ariwijayaputra/PeakGroundAcceleration/mqtt esp8266 accel/web/blueAbstract.jpg

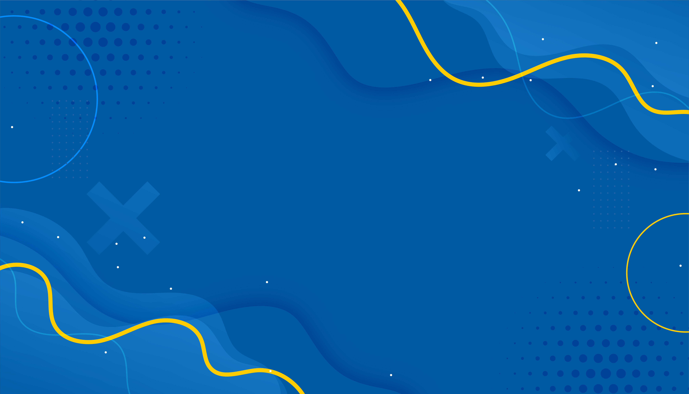
mqtt esp8266 accel/web/blueAbstract.jpg
