ariwijayaputra/PeakGroundAcceleration/mqtt esp8266 accel/web/dist/img/boxed-bg.jpg

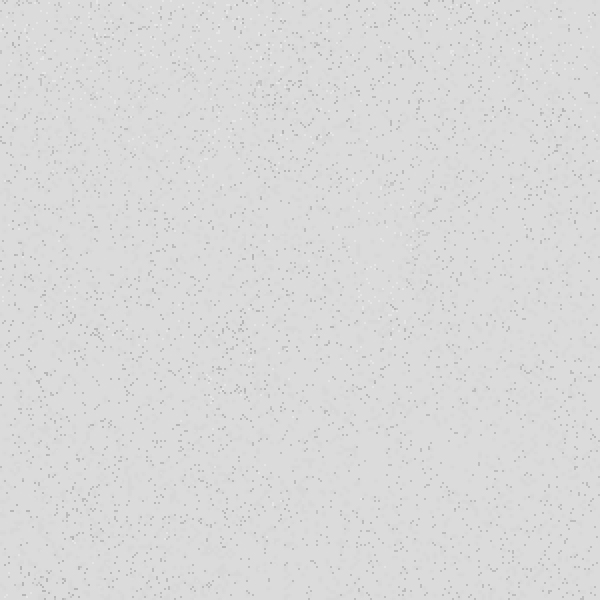
mqtt esp8266 accel/web/dist/img/boxed-bg.jpg
