ariwijayaputra/PeakGroundAcceleration/mqtt esp8266 accel/web/dist/img/photo1.png

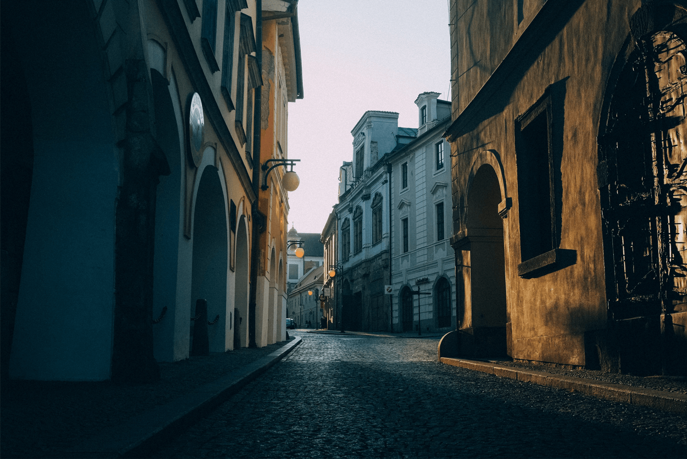
mqtt esp8266 accel/web/dist/img/photo1.png
