ariwijayaputra/PeakGroundAcceleration/mqtt esp8266 accel/web/dist/img/photo2.png

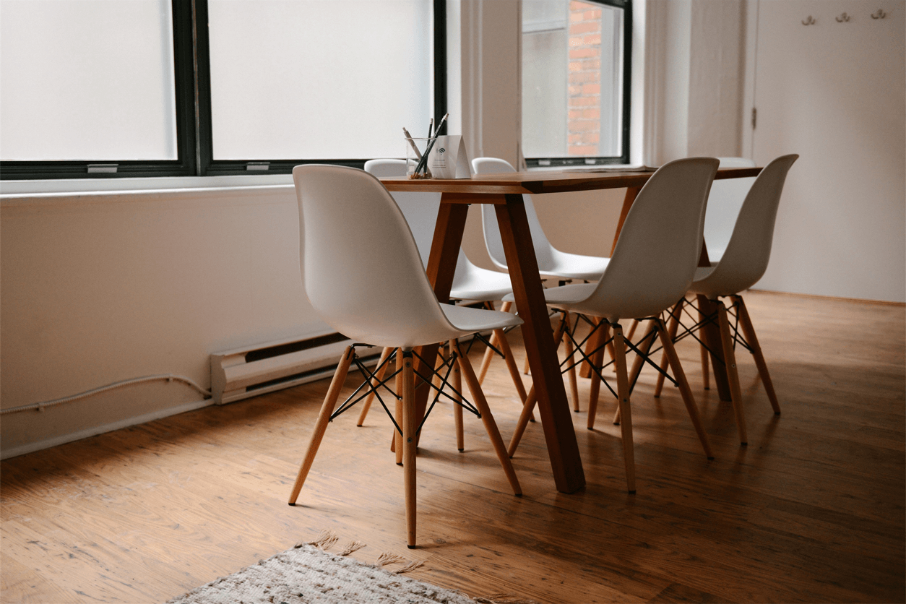
mqtt esp8266 accel/web/dist/img/photo2.png
