ariwijayaputra/PeakGroundAcceleration/mqtt esp8266 accel/web/dist/img/photo3.jpg

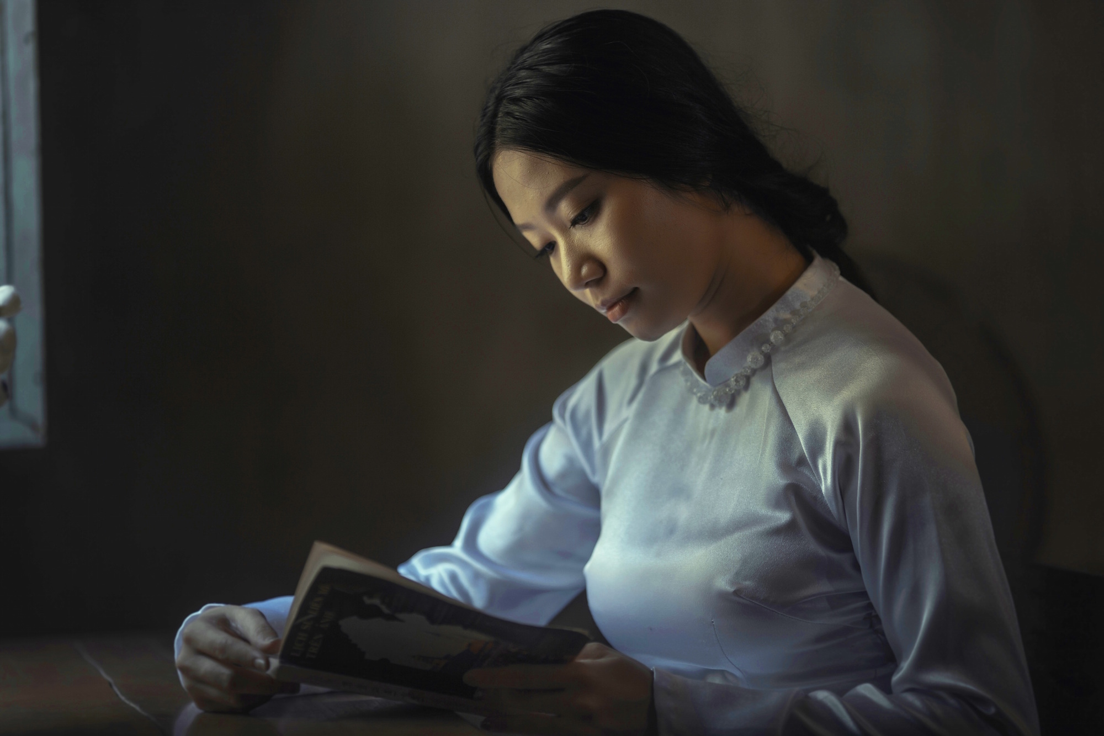
mqtt esp8266 accel/web/dist/img/photo3.jpg
