ariwijayaputra/PeakGroundAcceleration/mqtt esp8266 accel/web/dist/img/photo4.jpg

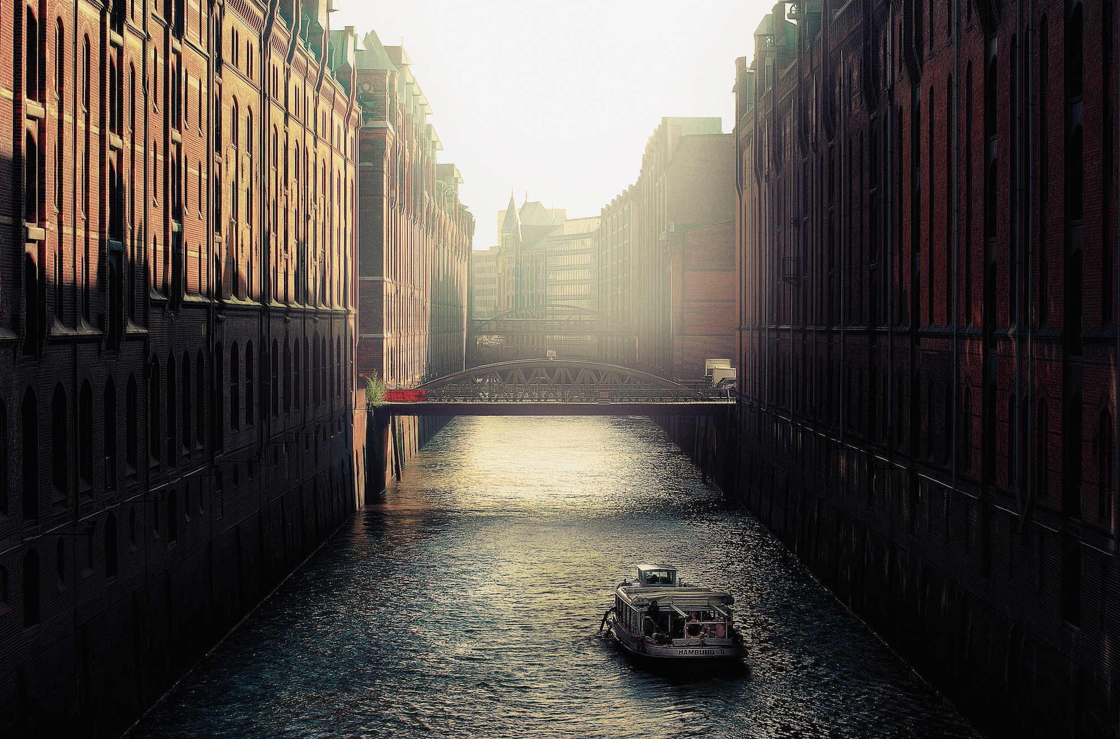
mqtt esp8266 accel/web/dist/img/photo4.jpg
