ariwijayaputra/PeakGroundAcceleration/mqtt esp8266 accel/web/dist/img/prod-5.jpg

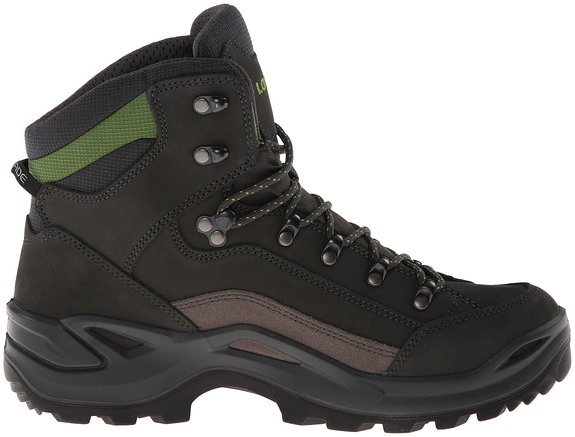
mqtt esp8266 accel/web/dist/img/prod-5.jpg
