ariwijayaputra/PeakGroundAcceleration/mqtt esp8266 accel/web/dist/img/user1-128x128.jpg

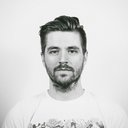
mqtt esp8266 accel/web/dist/img/user1-128x128.jpg
