ariwijayaputra/PeakGroundAcceleration/mqtt esp8266 accel/web/dist/img/user8-128x128.jpg

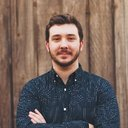
mqtt esp8266 accel/web/dist/img/user8-128x128.jpg
